martijnschouten/raspberry-bioamplifier/raspberry code/stdafx.h

#include <iostream>
#include <wiringPiSPI.h>
#include <unistd.h>
#include <wiringPi.h>
#include <string>
#include <cstring>
#include <cstdlib>
#include <cstring>
#include <boost/asio.hpp>
#include <iomanip>
#include <sstream>
#include <chrono>
#include <boost/circular_buffer.hpp>
